NathaelBoni/kerbal-kontroller/3DFiles/sas_buttons/radial_in_button.stl

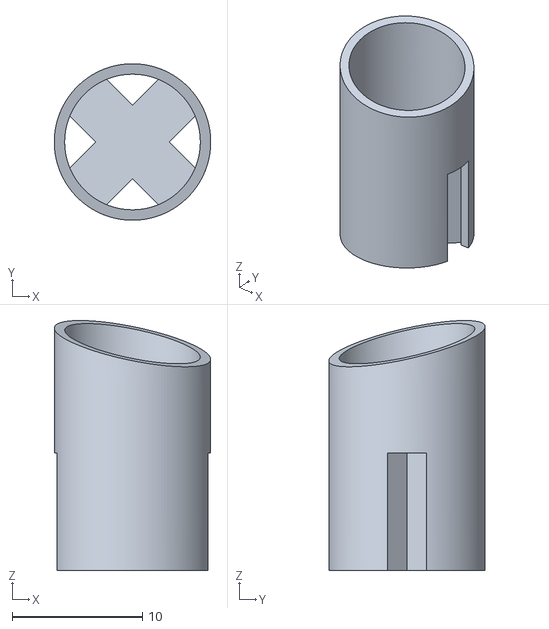
[picture p16: CAD file, 2021-08-15]
3DFiles/sas_buttons/radial_in_button.stl
12.0 x 12.0 x 19.2
