NathaelBoni/kerbal-kontroller/3DFiles/body/body_back_wall_game.stl

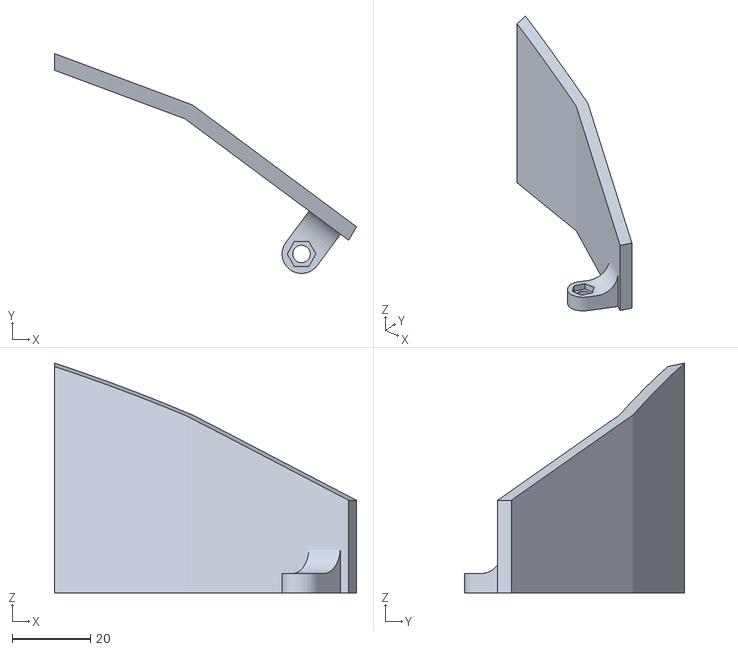
[picture p17: CAD file, 2021-08-15]
3DFiles/body/body_back_wall_game.stl
77.4 x 56.3 x 58.9
