NathaelBoni/kerbal-kontroller/3DFiles/game_buttons/quickload_button.stl

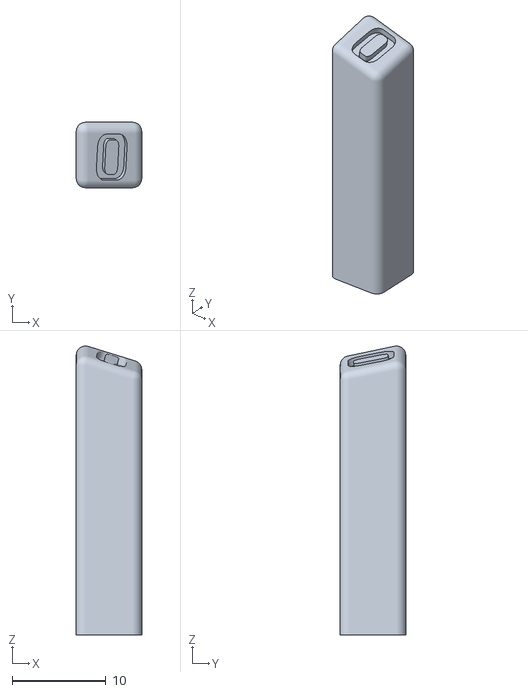
[picture p18: CAD file, 2021-08-15]
3DFiles/game_buttons/quickload_button.stl
7.00 x 7.00 x 30.8
