NathaelBoni/kerbal-kontroller/3DFiles/handle/pot_axis.stl

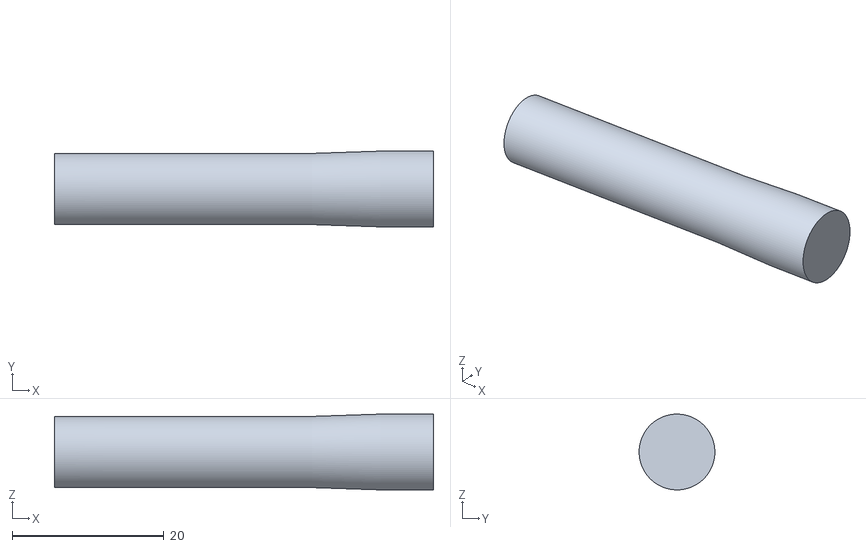
[picture p19: CAD file, 2021-08-15]
3DFiles/handle/pot_axis.stl
50.0 x 10.00 x 10.00
