NathaelBoni/kerbal-kontroller/3DFiles/joystick/precision_button_top.stl

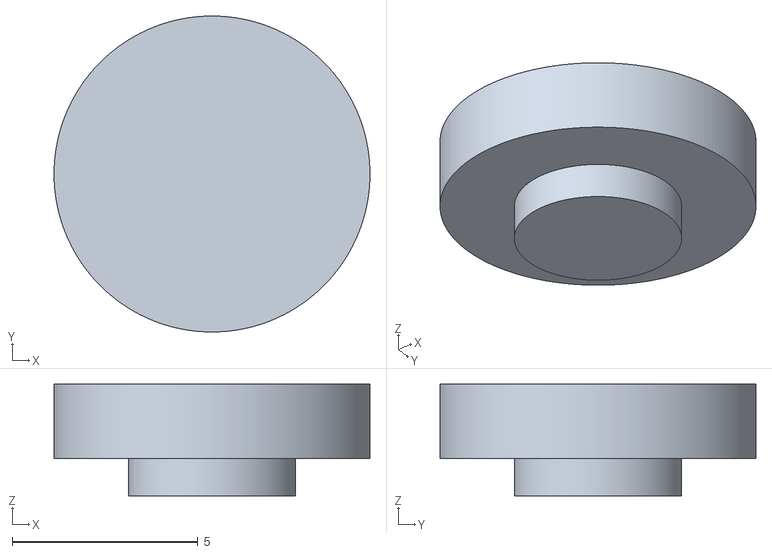
[picture p20: CAD file, 2021-08-15]
3DFiles/joystick/precision_button_top.stl
8.50 x 8.50 x 3.00
