NathaelBoni/kerbal-kontroller/3DFiles/sas_buttons/antinormal_button.stl

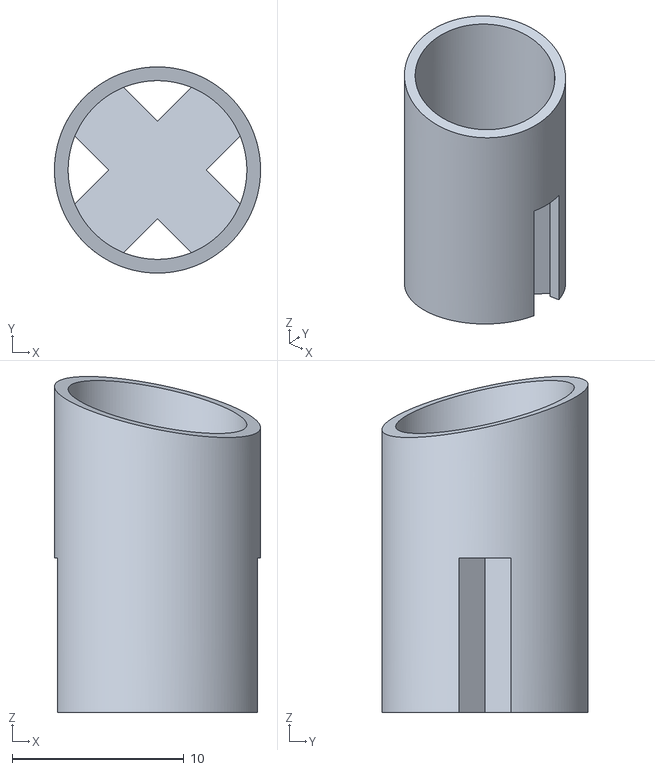
[picture p21: CAD file, 2021-08-15]
3DFiles/sas_buttons/antinormal_button.stl
12.0 x 12.0 x 19.6
