NathaelBoni/kerbal-kontroller/3DFiles/signs/sign_landing_gear.stl

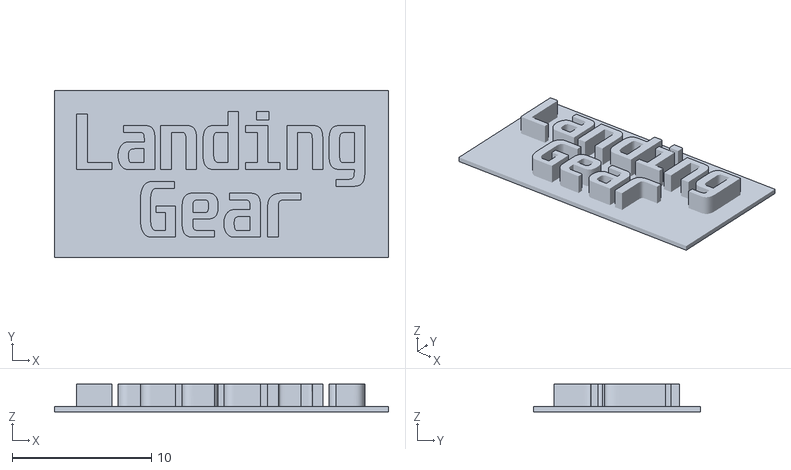
[picture p22: CAD file, 2021-08-15]
3DFiles/signs/sign_landing_gear.stl
24.0 x 12.0 x 2.00
