NathaelBoni/kerbal-kontroller/3DFiles/body/body_top_sas_btn.stl

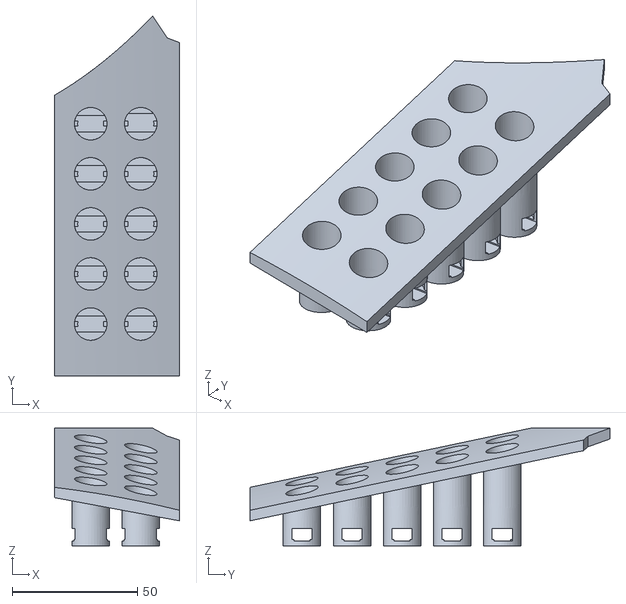
[picture p23: CAD file, 2021-08-15]
3DFiles/body/body_top_sas_btn.stl
50.0 x 143.8 x 47.0
