NathaelBoni/kerbal-kontroller/3DFiles/game_buttons/quicksave_button.stl

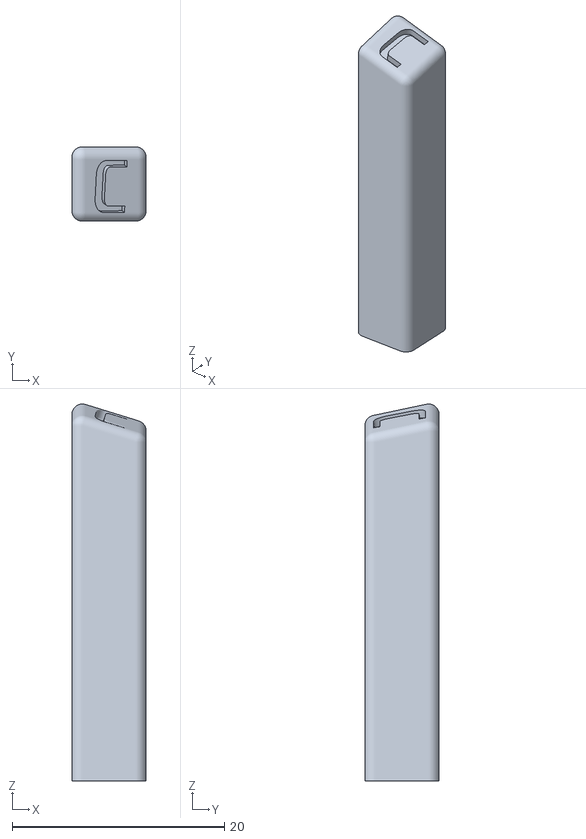
[picture p24: CAD file, 2021-08-15]
3DFiles/game_buttons/quicksave_button.stl
7.00 x 7.00 x 35.5
