NathaelBoni/kerbal-kontroller/3DFiles/joystick/left_joystick_top.stl

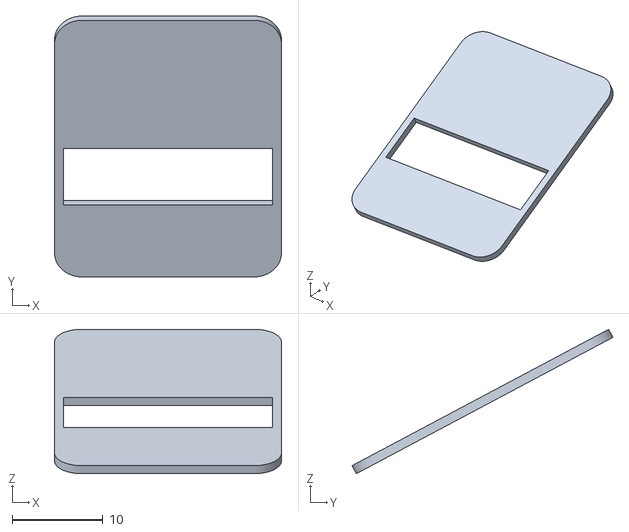
[picture p25: CAD file, 2021-08-15]
3DFiles/joystick/left_joystick_top.stl
25.0 x 28.7 x 15.9
