NathaelBoni/kerbal-kontroller/3DFiles/sas_buttons/prograde_button.stl

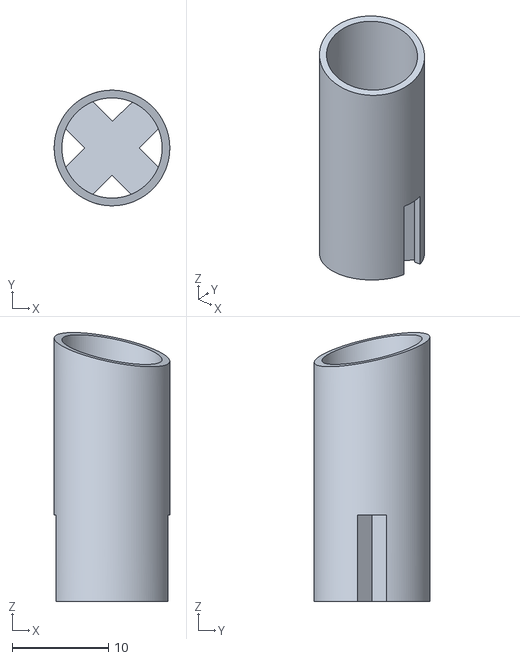
[picture p26: CAD file, 2021-08-15]
3DFiles/sas_buttons/prograde_button.stl
12.0 x 12.0 x 27.9
