NathaelBoni/kerbal-kontroller/3DFiles/signs/sign_break.stl

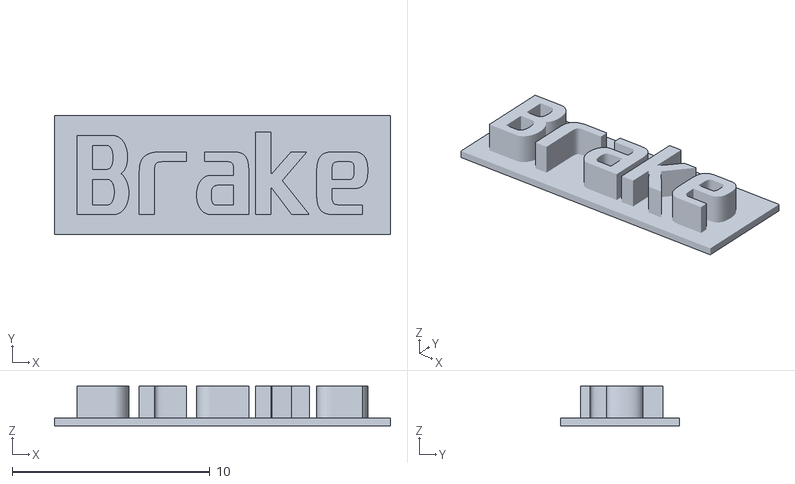
[picture p27: CAD file, 2021-08-15]
3DFiles/signs/sign_break.stl
17.0 x 6.00 x 2.00
