NathaelBoni/kerbal-kontroller/3DFiles/body/body_bottom_center.stl

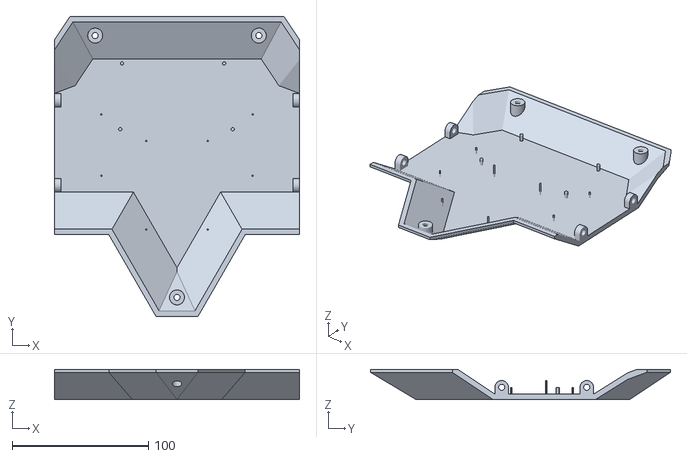
[picture p28: CAD file, 2021-08-15]
3DFiles/body/body_bottom_center.stl
180.0 x 220.0 x 22.1
