NathaelBoni/kerbal-kontroller/3DFiles/game_buttons/camera_button.stl

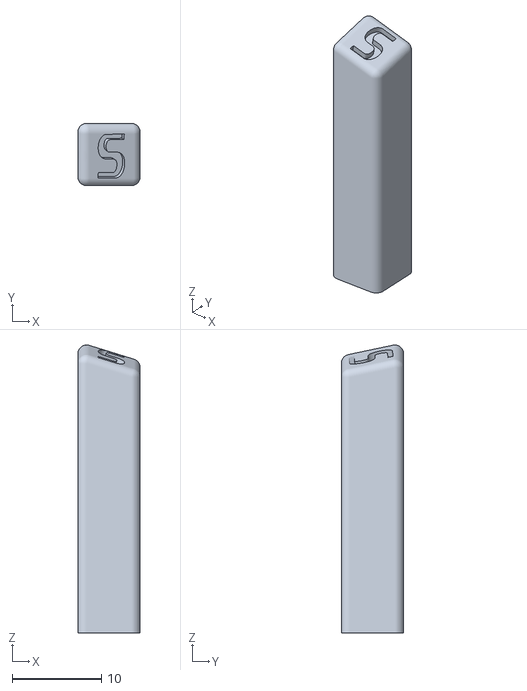
[picture p29: CAD file, 2021-08-15]
3DFiles/game_buttons/camera_button.stl
7.00 x 7.00 x 32.3
