NathaelBoni/kerbal-kontroller/3DFiles/sas_buttons/radial_out_button.stl

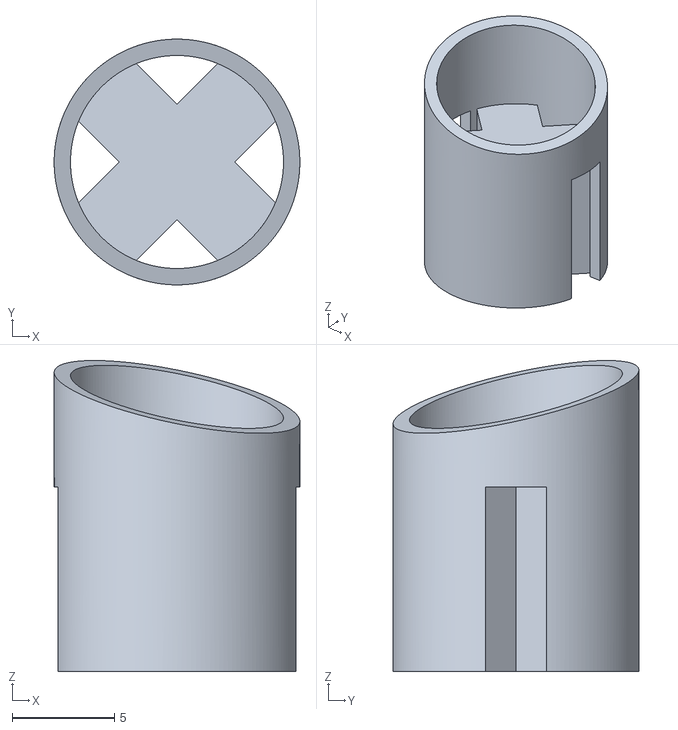
[picture p30: CAD file, 2021-08-15]
3DFiles/sas_buttons/radial_out_button.stl
12.0 x 12.0 x 15.2
