NathaelBoni/kerbal-kontroller/3DFiles/body/body_wall_center.stl

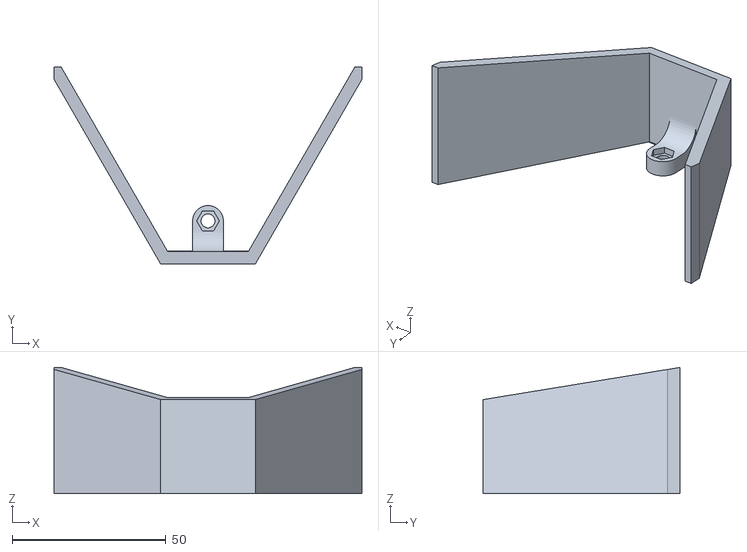
[picture p31: CAD file, 2021-08-15]
3DFiles/body/body_wall_center.stl
100.0 x 64.0 x 41.0
