NathaelBoni/kerbal-kontroller/3DFiles/game_buttons/orbital_view_button.stl

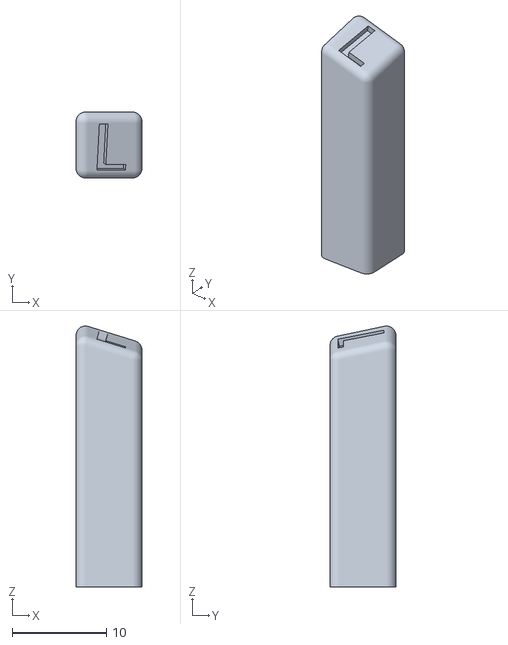
[picture p32: CAD file, 2021-08-15]
3DFiles/game_buttons/orbital_view_button.stl
7.00 x 7.00 x 27.7
