NathaelBoni/kerbal-kontroller/3DFiles/joystick/precision_button_bottom.stl

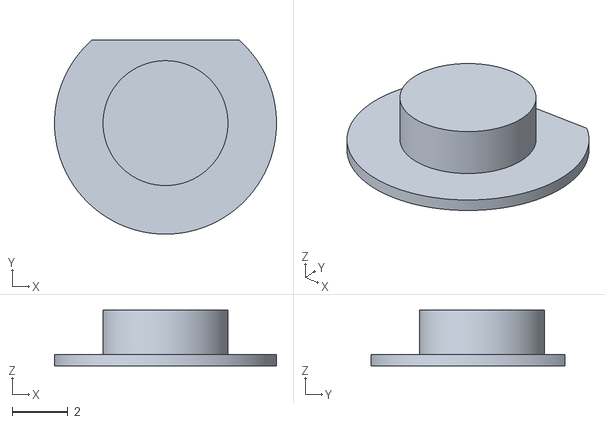
[picture p33: CAD file, 2021-08-15]
3DFiles/joystick/precision_button_bottom.stl
8.00 x 7.00 x 2.00
