NathaelBoni/kerbal-kontroller/3DFiles/body/body_top_game_btn.stl

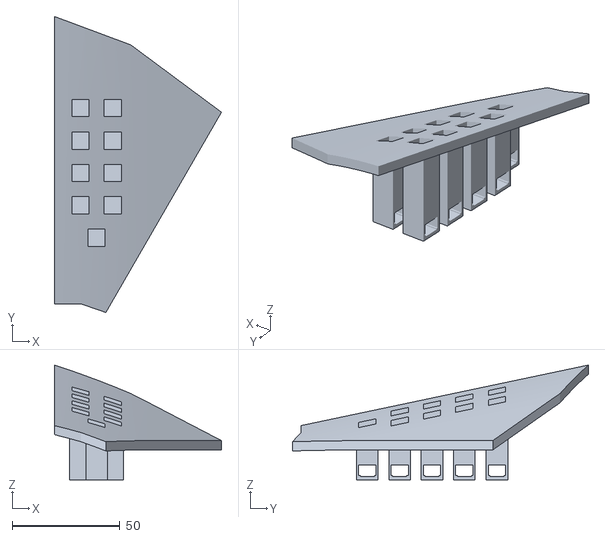
[picture p35: CAD file, 2021-08-15]
3DFiles/body/body_top_game_btn.stl
77.4 x 137.2 x 53.3
