NathaelBoni/kerbal-kontroller/3DFiles/game_buttons/next_vessel_button.stl

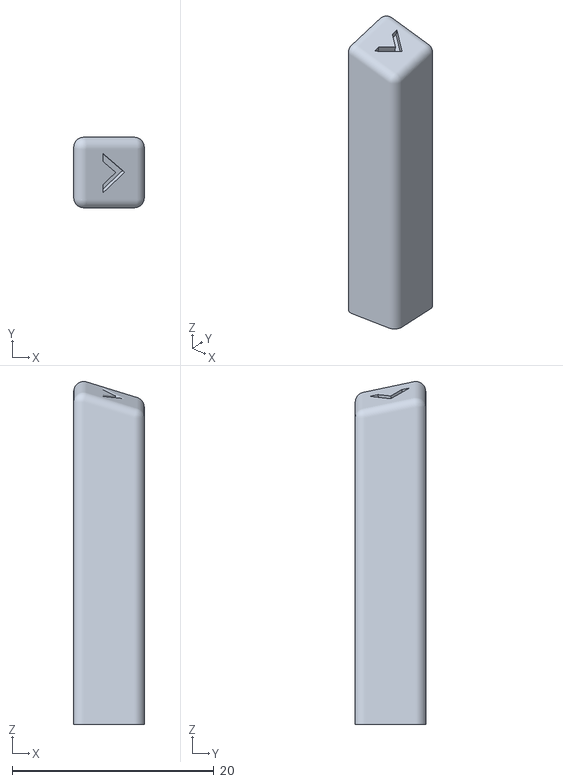
[picture p36: CAD file, 2021-08-15]
3DFiles/game_buttons/next_vessel_button.stl
7.00 x 7.00 x 34.0
