NathaelBoni/kerbal-kontroller/3DFiles/body/body_top_center.stl

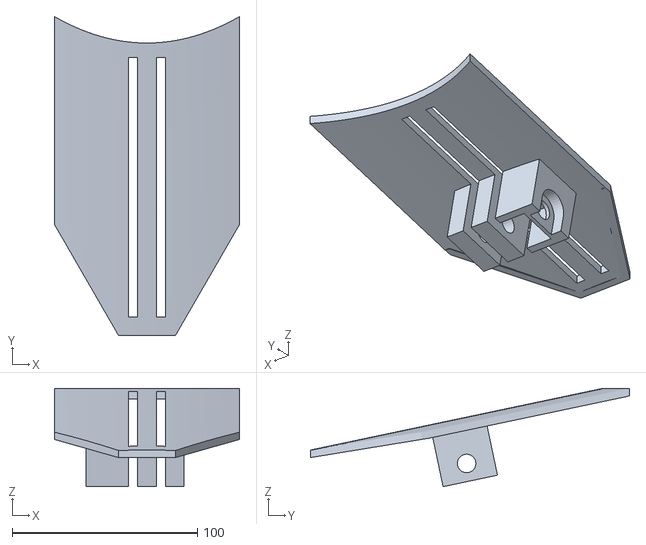
[picture p37: CAD file, 2021-08-15]
3DFiles/body/body_top_center.stl
100.0 x 172.1 x 53.0
