NathaelBoni/kerbal-kontroller/3DFiles/sas_buttons/normal_button_top.stl

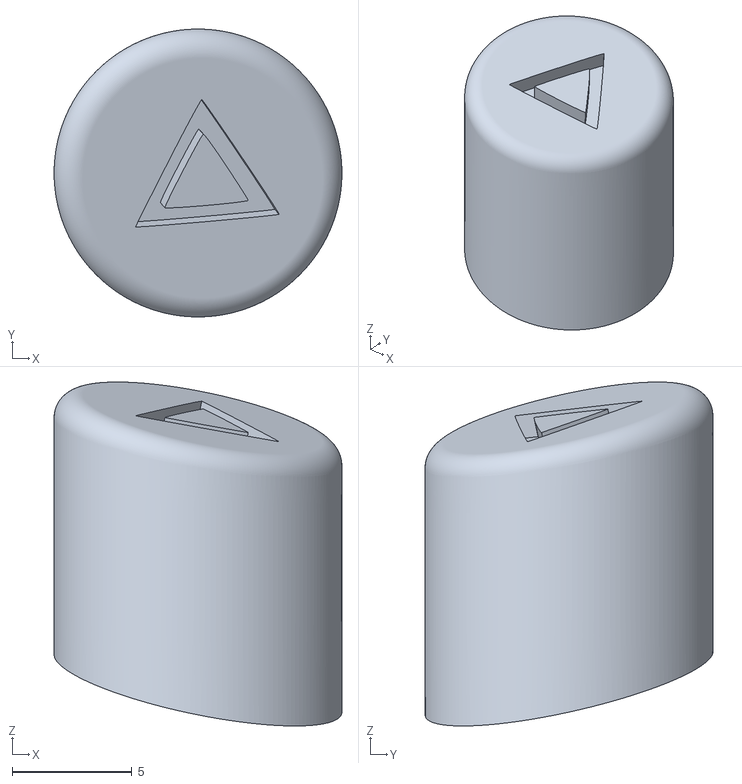
[picture p38: CAD file, 2021-08-15]
3DFiles/sas_buttons/normal_button_top.stl
12.0 x 12.0 x 14.3
