NathaelBoni/kerbal-kontroller/3DFiles/body/body_top_mech.stl

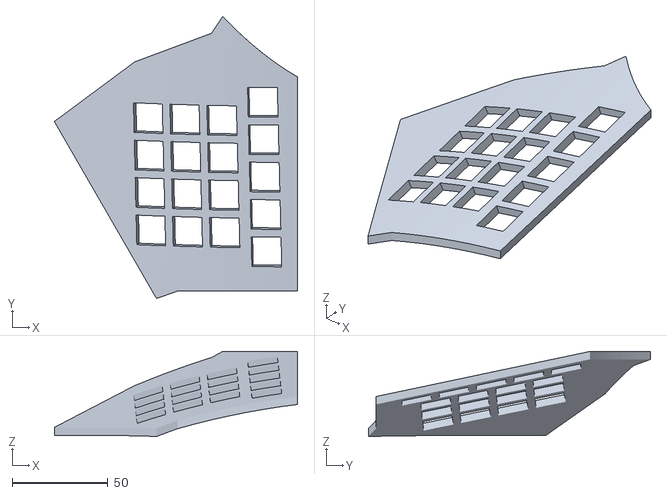
[picture p39: CAD file, 2021-08-15]
3DFiles/body/body_top_mech.stl
127.4 x 147.6 x 44.6
