NathaelBoni/kerbal-kontroller/3DFiles/sas_buttons/free_button.stl

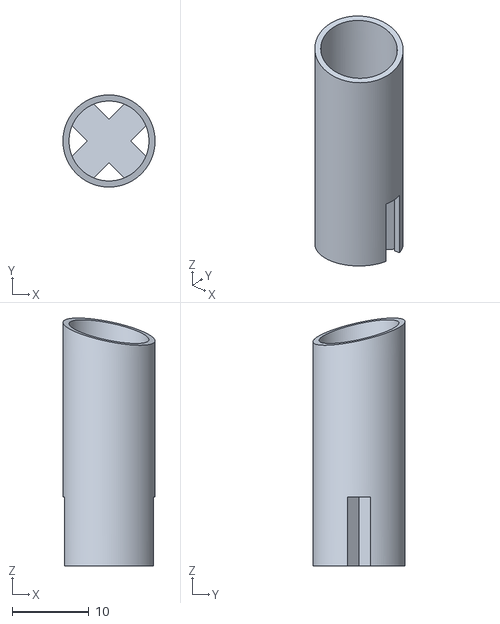
[picture p40: CAD file, 2021-08-15]
3DFiles/sas_buttons/free_button.stl
12.0 x 12.0 x 32.3
