NathaelBoni/kerbal-kontroller/3DFiles/body/body_front_wall_mech.stl

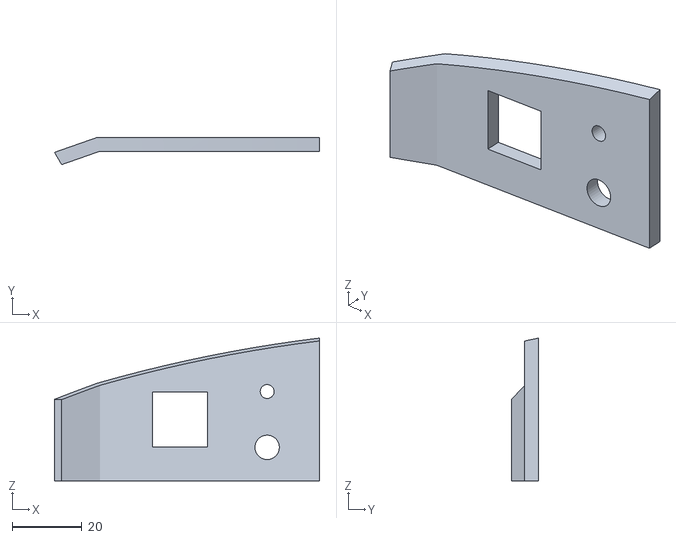
[picture p41: CAD file, 2021-08-15]
3DFiles/body/body_front_wall_mech.stl
75.9 x 7.83 x 41.0
