NathaelBoni/kerbal-kontroller/3DFiles/body/body_bottom_left.stl

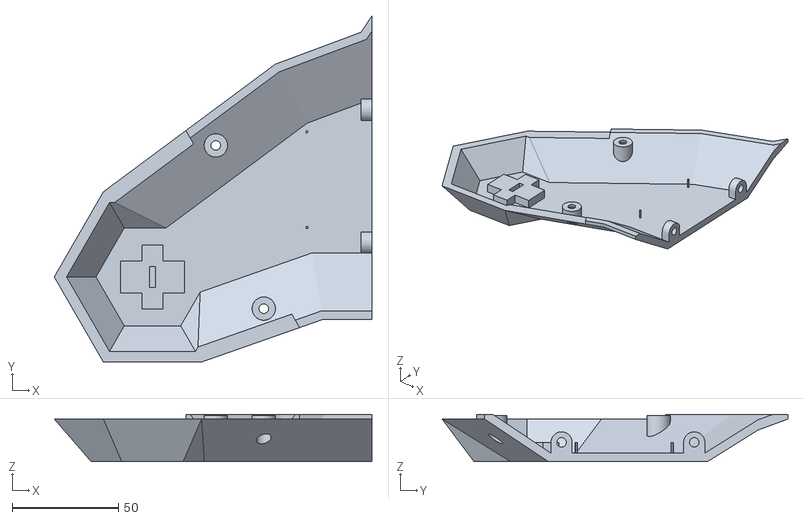
[picture p42: CAD file, 2021-08-15]
3DFiles/body/body_bottom_left.stl
149.3 x 162.7 x 22.1
