NathaelBoni/kerbal-kontroller/3DFiles/mech_keys/stage.stl

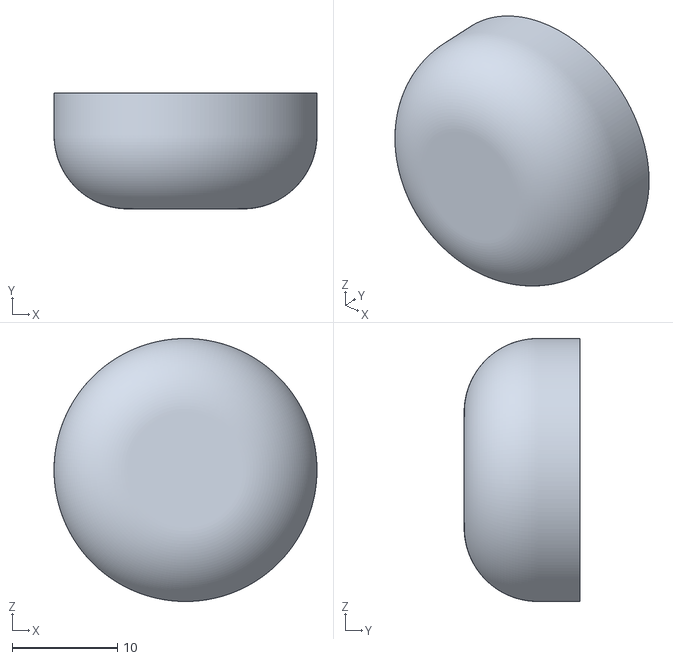
[picture p43: CAD file, 2021-08-15]
3DFiles/mech_keys/stage.stl
25.0 x 11.0 x 25.0
