NathaelBoni/kerbal-kontroller/3DFiles/sas_buttons/antitarget_button.stl

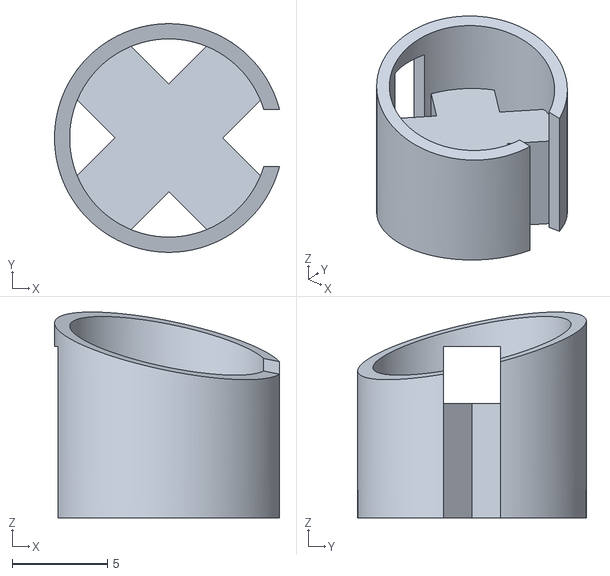
[picture p44: CAD file, 2021-08-15]
3DFiles/sas_buttons/antitarget_button.stl
11.8 x 12.0 x 10.8
