NathaelBoni/kerbal-kontroller/3DFiles/body/body_back_wall_sas.stl

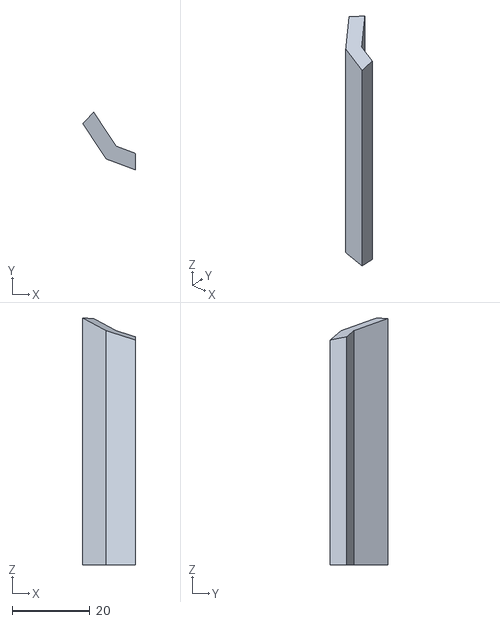
[picture p45: CAD file, 2021-08-15]
3DFiles/body/body_back_wall_sas.stl
13.6 x 14.9 x 63.7
