NathaelBoni/kerbal-kontroller/3DFiles/body/body_top_switch.stl

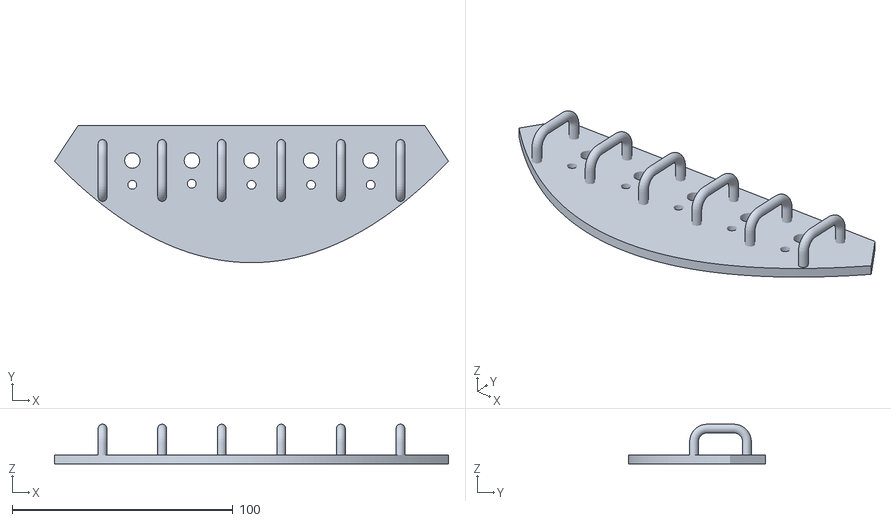
[picture p46: CAD file, 2021-08-15]
3DFiles/body/body_top_switch.stl
178.5 x 62.2 x 18.0
