NathaelBoni/kerbal-kontroller/3DFiles/sas_buttons/radial_out_button_top.stl

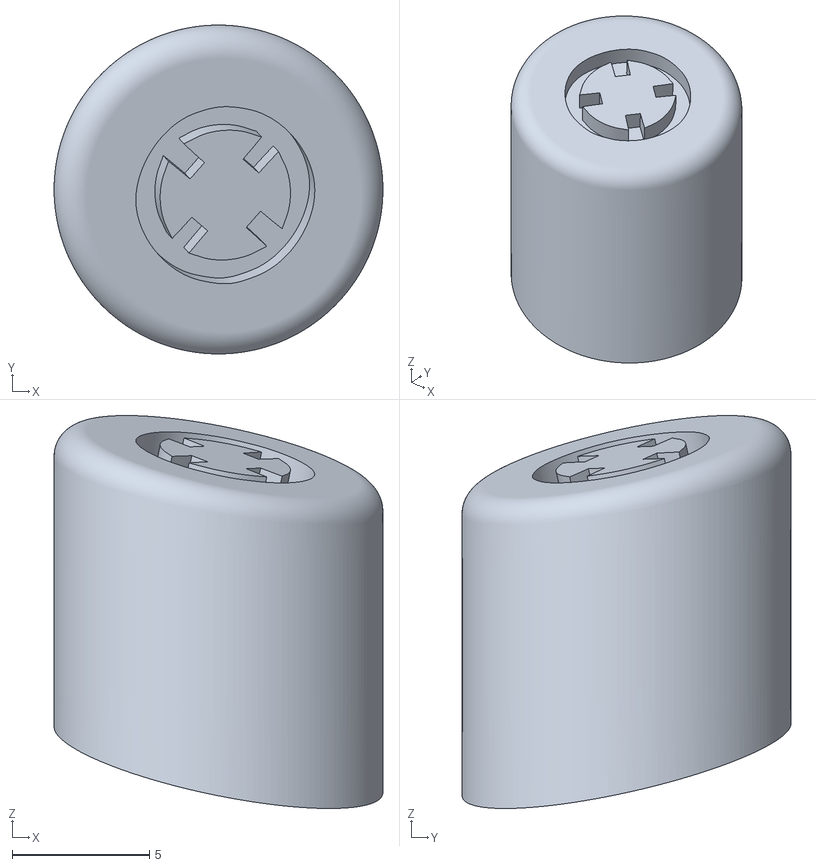
[picture p47: CAD file, 2021-08-15]
3DFiles/sas_buttons/radial_out_button_top.stl
12.0 x 12.0 x 14.3
