NathaelBoni/kerbal-kontroller/3DFiles/body/body_front_wall_game.stl

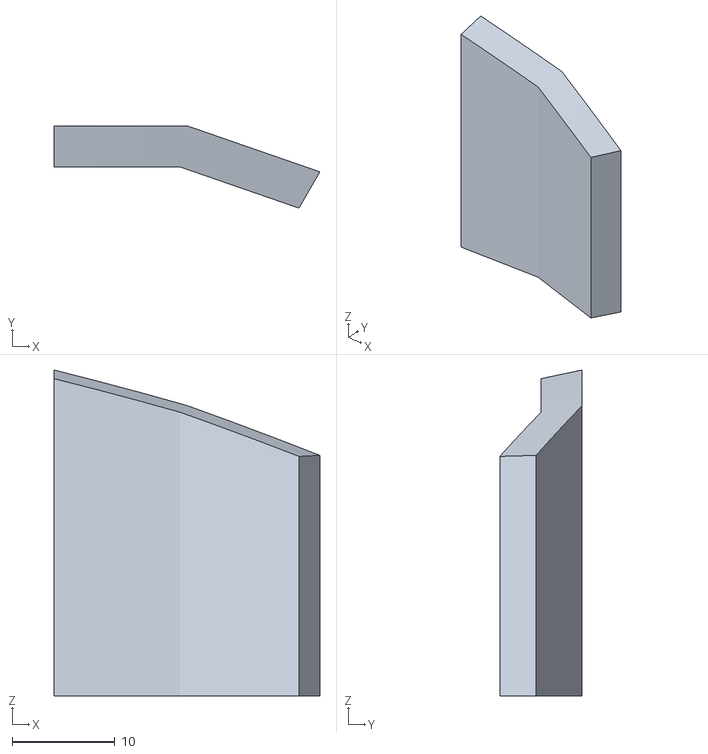
[picture p48: CAD file, 2021-08-15]
3DFiles/body/body_front_wall_game.stl
25.8 x 8.00 x 31.7
