NathaelBoni/kerbal-kontroller/3DFiles/body/body_wall_switch.stl

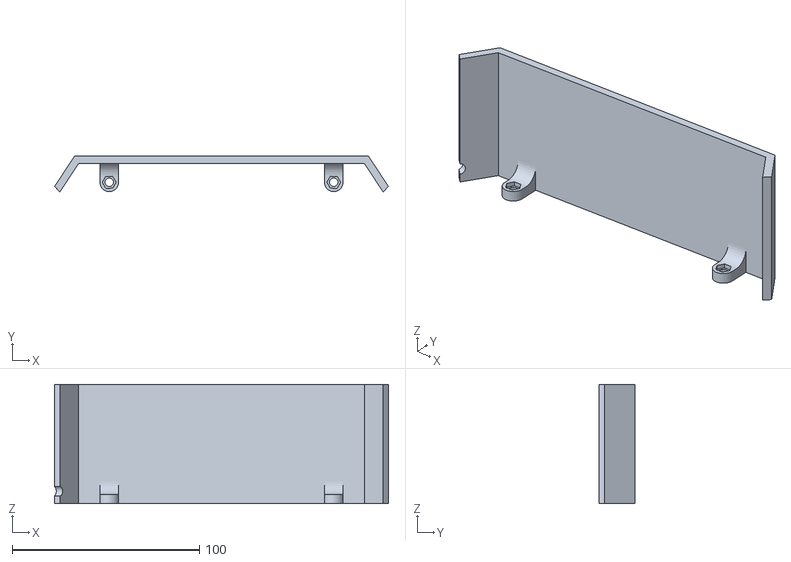
[picture p49: CAD file, 2021-08-15]
3DFiles/body/body_wall_switch.stl
178.5 x 19.1 x 63.9
