NathaelBoni/kerbal-kontroller/ArduinoKode/ActionHelper.h

#ifndef _action_helper_h
#define _action_helper_h

void ReadActionButtons();
void ReadKeys();
void ReadSASButtons();
void ReadGameButtons();
void ReadSwitches();
void ReadAbortStage();
void ReadPrecisionButtons();

#endif
